radhoo/uradmonitor_smoggie/pcb/005/pics/sch_v5.png

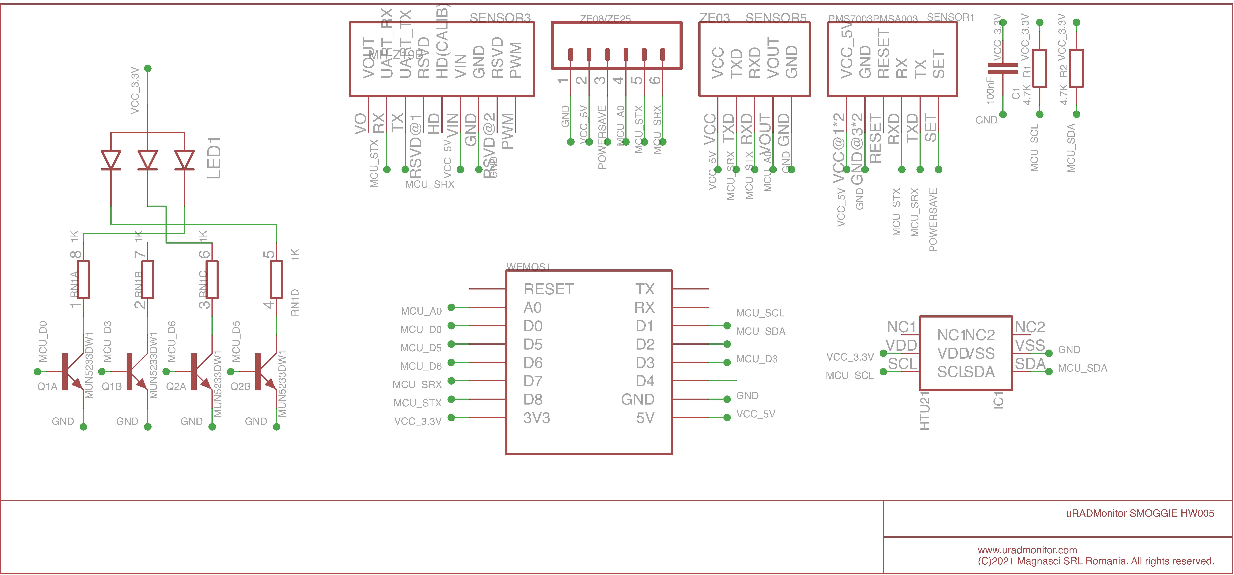
pcb/005/pics/sch_v5.png
