radhoo/uradmonitor_smoggie/pics/model_SMOGGIE.jpg

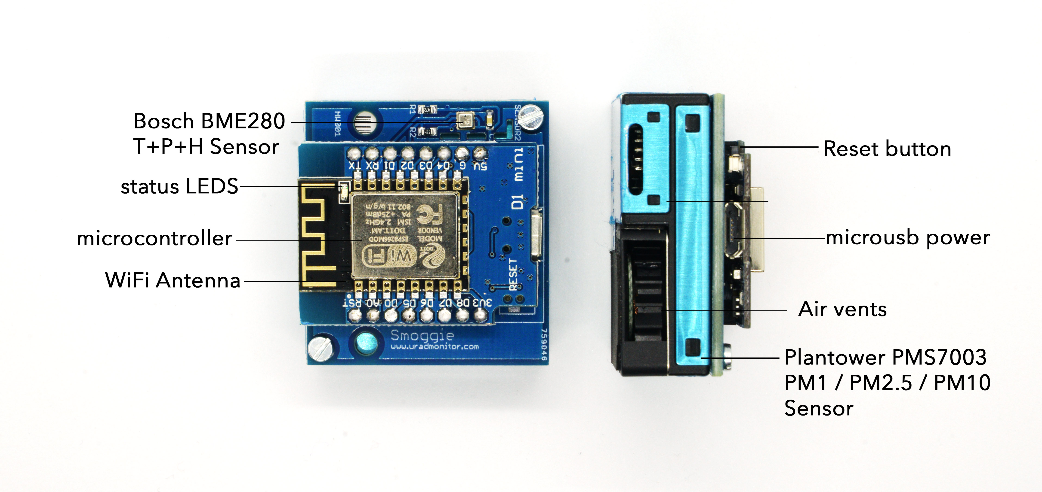
pics/model_SMOGGIE.jpg
