radhoo/uradmonitor_smoggie/pics/smoggie_v4.jpg

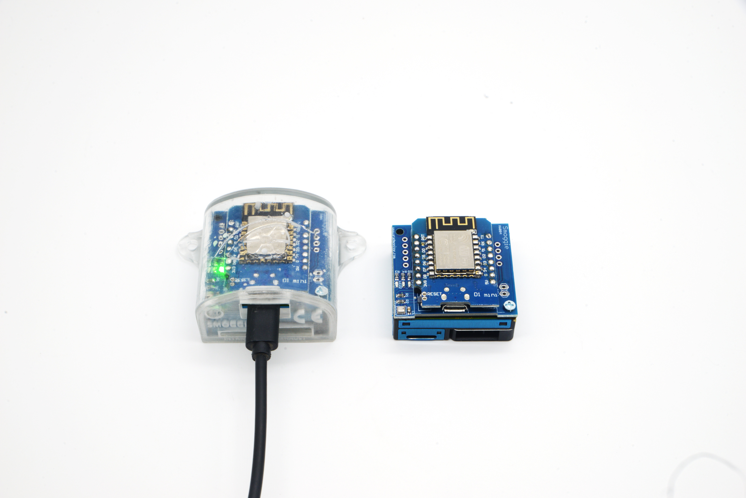
pics/smoggie_v4.jpg
