radhoo/uradmonitor_smoggie/pcb/005/pics/bom.png

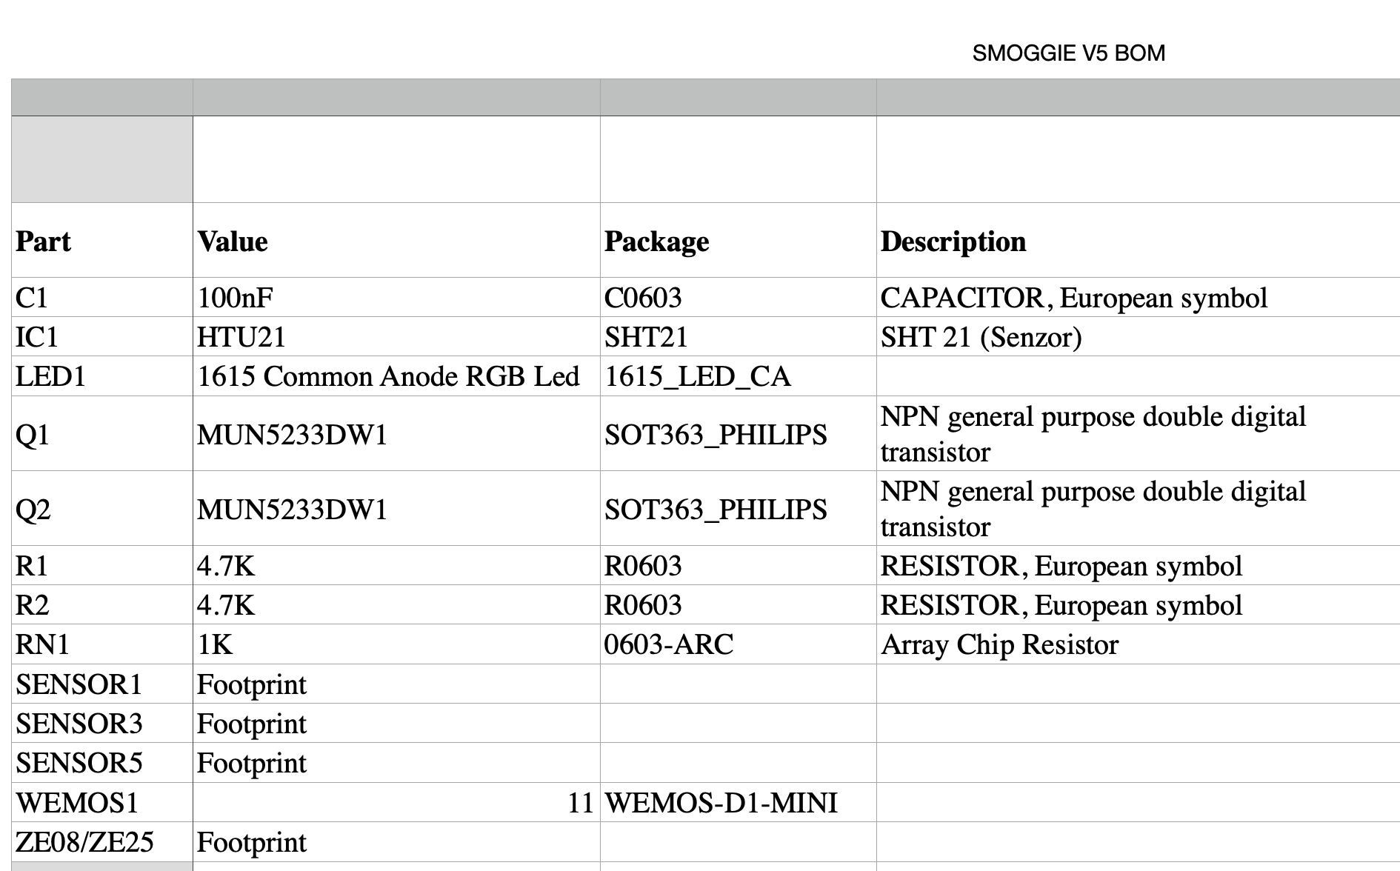
pcb/005/pics/bom.png
